SonarSquad/OASIS/MCU_ATmega4809/Test.c

/*
 * Created: 05.03.2020 15:34:44
 * Edited: 22.04:2020 09:13:37
 * Author: Torbjørn Wilson
 *
 *down-chirp from 208kHz to 192kHz
 *208333,3333Hz
 *206185,5670Hz
 *204081,6327Hz
 *202020,2020Hz
 *200000,0000Hz
 *198019,8020Hz
 *196078,4314Hz
 *194174,7573Hz
 *192307,6923Hz
 */
#ifndef F_CPU
#define F_CPU 20000000
#endif

#define OFF_PF5		PORTF_OUTCLR = PIN5_bm
#define ON_PF5		PORTF_OUTSET = PIN5_bm
#define OFF_PF4		PORTF_OUTCLR = PIN4_bm
#define ON_PF4		PORTF_OUTSET = PIN4_bm

#include <avr/io.h>
#include <util/delay.h>
#include <avr/interrupt.h>
#include <util/delay_basic.h>

void chirp(void)
{
OFF_PF4;
OFF_PF5;

//96 clk gives 208333,3333 Hz
//48 commands
ON_PF4;
OFF_PF4;
OFF_PF4;
OFF_PF4;
ON_PF4;
ON_PF4;
OFF_PF4;
OFF_PF4;
OFF_PF4;
ON_PF4;
ON_PF4;
ON_PF4;
OFF_PF4;
OFF_PF4;
OFF_PF4;
ON_PF4;
ON_PF4;
ON_PF4;
ON_PF4;
OFF_PF4;
OFF_PF4;
ON_PF4;
ON_PF4;
ON_PF4;
ON_PF4;
ON_PF4;
ON_PF4;
OFF_PF4;
OFF_PF4;
ON_PF4;
ON_PF4;
ON_PF4;
ON_PF4;
OFF_PF4;
OFF_PF4;
OFF_PF4;
ON_PF4;
ON_PF4;
ON_PF4;
OFF_PF4;
OFF_PF4;
OFF_PF4;
ON_PF4;
ON_PF4;
OFF_PF4;
OFF_PF4;
ON_PF4;
OFF_PF4;
//Second periode 208333,3333 Hz
//48 commands
ON_PF5;
OFF_PF5;
OFF_PF5;
OFF_PF5;
ON_PF5;
ON_PF5;
OFF_PF5;
OFF_PF5;
OFF_PF5;
ON_PF5;
ON_PF5;
ON_PF5;
OFF_PF5;
OFF_PF5;
OFF_PF5;
ON_PF5;
ON_PF5;
ON_PF5;
ON_PF5;
OFF_PF5;
OFF_PF5;
ON_PF5;
ON_PF5;
ON_PF5;
ON_PF5;
ON_PF5;
ON_PF5;
OFF_PF5;
OFF_PF5;
ON_PF5;
ON_PF5;
ON_PF5;
ON_PF5;
OFF_PF5;
OFF_PF5;
OFF_PF5;
ON_PF5;
ON_PF5;
ON_PF5;
OFF_PF5;
OFF_PF5;
OFF_PF5;
ON_PF5;
ON_PF5;
OFF_PF5;
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
OFF_PF5;
OFF_PF5; //extra 2
ON_PF5;
ON_PF5;
ON_PF5;
ON_PF5;
ON_PF5;
ON_PF5;
OFF_PF5;
OFF_PF5;
OFF_PF5; //extra 4
ON_PF5;
ON_PF5;
ON_PF5;
ON_PF5;
OFF_PF5;
OFF_PF5;
OFF_PF5;
ON_PF5;
ON_PF5;
ON_PF5;
OFF_PF5;
OFF_PF5;
OFF_PF5;
ON_PF5;
ON_PF5;
OFF_PF5;
OFF_PF5;
OFF_PF5; //extra 6
ON_PF5;
OFF_PF5;
};
